astralien3000/buggybot2/soft/app/embed-io/conanfile.py

from conans import ConanFile, CMake, Embedded

class AversivePlusPlusProjectConan(ConanFile):
    name="embed-io"
    version="0.1"
    settings = "os", "compiler", "build_type", "arch", "target"
    requires = (
        "AversivePlusPlus/0.1@AversivePlusPlus/dev",
        "toolchain-switch/0.1@AversivePlusPlus/dev",
        "hal-switch/0.1@AversivePlusPlus/dev",
        "stream-hal/0.1@AversivePlusPlus/dev",
        "device-hal/0.1@AversivePlusPlus/dev",

        "buggybot-protocol/0.1@AversivePlusPlus/dev",
        "device-buggybot-adm2560/0.1@AversivePlusPlus/dev",
        )
    generators = "cmake", "txt"

    def imports(self):
        self.copy("*.cmake", dst="toolchain", src="toolchain")
        self.copy("*.ld", dst="toolchain/linker", src="linker")

    def build(self):
        cmake = CMake(self.settings)
        embed = Embedded(self.settings)
        toolchain = '-DCMAKE_TOOLCHAIN_FILE=toolchain/%s.cmake' % embed.microcontroller()

        self.run('cmake "%s" %s %s' % (self.conanfile_directory, cmake.command_line, toolchain))
        self.run('cmake --build . %s' % cmake.build_config)
