astralien3000/buggybot2/soft/test/iotlab/embed-full/src/servo_collection/servo_handler.cpp

#include "servo_handler.hpp"
#include "../model.hpp"
#include <stream/buffer_stream.hpp>
#include <stream/formatted_stream.hpp>
#include <stdio.h>

#include <xtimer.h>

static const char* _prefix = "feetech";

enum class ServoReg {
  NONE,
  POSITION,
  TORQUE_EN,
  ID,
};

static bool _is_uri_path(coap::OptionReader& opt) {
  return opt.getNum() == coap::OptionNum::URI_PATH;
}

static bool _is_uri_path(coap::OptionReader& opt, const char* str) {
  return _is_uri_path(opt) &&
      strncmp(str, (const char*)opt.getValue(), opt.getLength()) == 0;
}

static bool _get_request_params(const coap::PacketReader& req, uint8_t& id_out, ServoReg& reg_out, coap::MethodCode& method_out) {
  int state = 0;
  
  method_out = req.getMethodCode();
  for(auto it = req.getOptionsBegin() ; it != req.getOptionsEnd() ; it++) {
    auto opt = *it;
    if(state == 0) {
      if(_is_uri_path(opt, _prefix)) {
        state++;
      }
    }
    else if(state == 1) {
      if(_is_uri_path(opt)) {
        Aversive::Stream::BufferStream<64> ss;
        Aversive::Stream::FormattedStreamDecorator<decltype(ss)>& fss = formatted(ss);
        ss.write((const char*)opt.getValue(), opt.getLength());
        ss.write((const char*)"\0", 1);
        fss >> id_out;
        state++;
      }
      else {
        return false;
      }
    }
    else if(state == 2) {
      if(_is_uri_path(opt, "id")) {
        reg_out = ServoReg::ID;
        state++;
      }
      else if(_is_uri_path(opt, "torque_en")) {
        reg_out = ServoReg::TORQUE_EN;
        state++;
      }
      else if(_is_uri_path(opt, "position")) {
        reg_out = ServoReg::POSITION;
        state++;
      }
      else {
        return false;
      }
    }
    else {
      if(_is_uri_path(opt)) {
        return false;
      }
      else {
        return true;
      }
    }
  }
  return state == 3;
}

template<typename T>
static coap::Error _content(const coap::PacketReader& req, coap::PacketBuilder& res, coap::ResponseCode code, T content) {
  Aversive::Stream::BufferStream<16> ss;
  Aversive::Stream::FormattedStreamDecorator<decltype(ss)>& fss = formatted(ss);

  fss << content;

  return res.makeResponse(req, code, coap::ContentType::TEXT_PLAIN, ss);
}

template<typename T>
static T _to_int(const uint8_t* str, size_t len) {
  Aversive::Stream::BufferStream<16> ss;
  Aversive::Stream::FormattedStreamDecorator<decltype(ss)>& fss = formatted(ss);
  
  ss.write((const char*)str, (uint16_t)len);
  ss.write((const char*)"\0", 1);
  T ret = 0;
  fss >> ret;
  return ret;
}

coap::ReturnCode ServoHandler::handle(const coap::PacketReader& req, coap::PacketBuilder& res) {
  uint8_t id = 0;
  ServoReg sreg = ServoReg::NONE;
  coap::MethodCode method = coap::MethodCode::GET;
  if(_get_request_params(req, id, sreg, method)) {
    if(sreg == ServoReg::ID) {
      if(method == coap::MethodCode::GET) {
        if(_content(req, res, coap::ResponseCode::CONTENT, id) == coap::Error::NONE) {
          return coap::ReturnCode::SEND;
        }
        else {
          return coap::ReturnCode::ERROR;
        }
      }
      else {
        if(res.makeResponse(req, coap::ResponseCode::METHOD_NOT_ALLOWED) == coap::Error::NONE) {
          return coap::ReturnCode::SEND;
        }
        else {
          return coap::ReturnCode::ERROR;
        }
      }
    }
    else if(sreg == ServoReg::POSITION) {
      if(method == coap::MethodCode::GET) {
        if(_content(req, res, coap::ResponseCode::CONTENT, sc.getPosition(id)) == coap::Error::NONE) {
          return coap::ReturnCode::SEND;
        }
        else {
          return coap::ReturnCode::ERROR;
        }
      }
      else if(method == coap::MethodCode::PUT) {
        uint16_t val = _to_int<uint16_t>(req.getPayload(), req.getPayloadLength());
        sc.setPosition(id, val);
        if(_content(req, res, coap::ResponseCode::CHANGED, val) == coap::Error::NONE) {
          return coap::ReturnCode::SEND;
        }
        else {
          return coap::ReturnCode::ERROR;
        }
      }
      else {
        if(res.makeResponse(req, coap::ResponseCode::METHOD_NOT_ALLOWED) == coap::Error::NONE) {
          return coap::ReturnCode::SEND;
        }
        else {
          return coap::ReturnCode::ERROR;
        }
      }
    }
    else if(sreg == ServoReg::TORQUE_EN) {
      if(method == coap::MethodCode::GET) {
        if(_content(req, res, coap::ResponseCode::CONTENT, (uint8_t)sc.isTorqueEnabled(id)) == coap::Error::NONE) {
          return coap::ReturnCode::SEND;
        }
        else {
          return coap::ReturnCode::ERROR;
        }
      }
      else if(method == coap::MethodCode::PUT) {
        uint8_t val = _to_int<uint8_t>(req.getPayload(), req.getPayloadLength());
        if(val == 1) sc.enableTorque(id);
        else sc.disableTorque(id);
        if(_content(req, res, coap::ResponseCode::CHANGED, val) == coap::Error::NONE) {
          return coap::ReturnCode::SEND;
        }
        else {
          return coap::ReturnCode::ERROR;
        }
      }
      else {
        if(res.makeResponse(req, coap::ResponseCode::METHOD_NOT_ALLOWED) == coap::Error::NONE) {
          return coap::ReturnCode::SEND;
        }
        else {
          return coap::ReturnCode::ERROR;
        }
      }
    }
  }
  
  return coap::ReturnCode::NEXT_HANDLER;
}

static bool _try_add_page(char* &cur, size_t size, uint8_t i, const char* page) {
  Aversive::Stream::BufferStream<64> ss;
  Aversive::Stream::FormattedStreamDecorator<decltype(ss)>& fss = formatted(ss);
  
  fss << "</" << _prefix << "/" << (uint16_t)i << "/" << page << ">;ct=0,";
  uint16_t s =  ss.readable();
  if(s < size) {
    ss.read((char*)cur, s);
    cur += s;
    size -= s;
  }
  else {
    return false;
  }
  return true;
}

namespace coap {
size_t SimpleDiscoveryInputStream<ServoHandler>::read(char* buffer, size_t size) {
  char* cur = (char*)buffer;
  
  for(uint8_t i = 0 ; i < 15 ; i++) {
    if(sc.ping(i)) {
      if(!_try_add_page(cur, size, i, "id")) {
        return (size_t)((char*)cur - buffer);
      }

      if(!_try_add_page(cur, size, i, "torque_en")) {
        return (size_t)((char*)cur - buffer);
      }

      if(!_try_add_page(cur, size, i, "position")) {
        return (size_t)((char*)cur - buffer);
      }
    }
    xtimer_usleep(200);
  }
  
  return (size_t)((char*)cur - buffer);
}
}
