astralien3000/buggybot2/soft/test/iotlab/embed-full/src/servo_collection/servo_handler.hpp

#include <coap/coap.hpp>

class ServoHandler {
public:
  inline ServoHandler(void) {}

  coap::ReturnCode handle(const coap::PacketReader& req, coap::PacketBuilder& res);
};

namespace coap {
template<>
class SimpleDiscoveryInputStream<ServoHandler> : ServoHandler {
public:
  size_t read(char* buffer, size_t size);
};
}
