astralien3000/buggybot2/soft/test/iotlab/embed-full/src/servo_mapper/config_handler.hpp

#include <coap/coap.hpp>

class ConfigHandler {
public:
  inline ConfigHandler(void) {}

  coap::ReturnCode handle(const coap::PacketReader& req, coap::PacketBuilder& res);
};

namespace coap {
template<>
class SimpleDiscoveryInputStream<ConfigHandler> : ConfigHandler {
public:
  size_t read(char* buffer, size_t size);
};
}
