astralien3000/buggybot2/soft/test/iotlab/embed-full/src/servo_mapper/label_handler.hpp

#include <coap/coap.hpp>

class LabelHandler {
public:
  inline LabelHandler(void) {}

  coap::ReturnCode handle(const coap::PacketReader& req, coap::PacketBuilder& res);
};

namespace coap {
template<>
class SimpleDiscoveryInputStream<LabelHandler> : LabelHandler {
public:
  size_t read(char* buffer, size_t size);
};
}
